05TapPau/HOTAS/Images/Frames.jpg

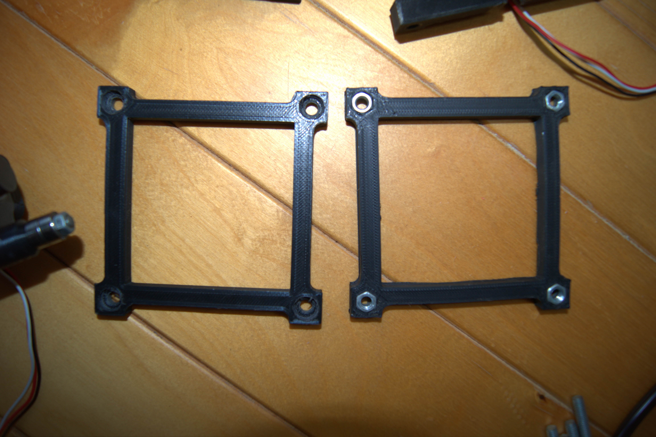
Images/Frames.jpg
