05TapPau/HOTAS/Images/Shell_poti.jpg

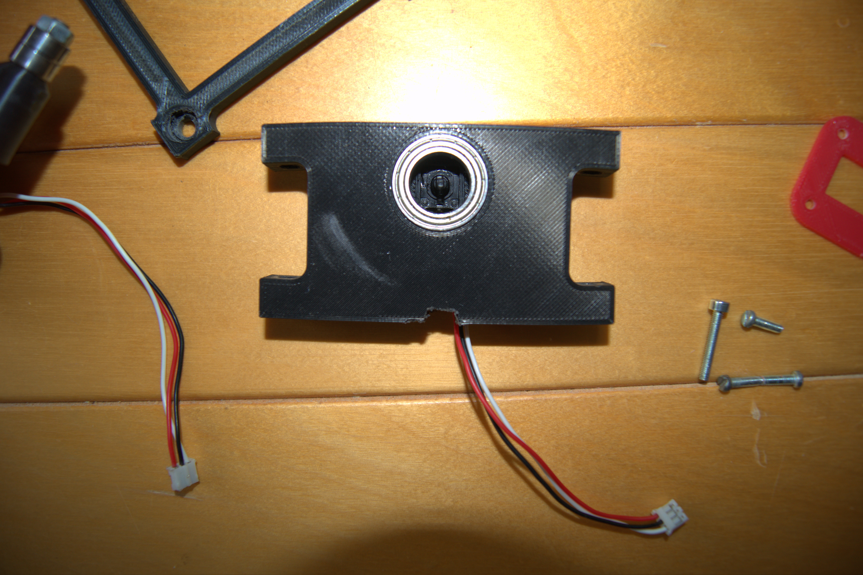
Images/Shell_poti.jpg
