05TapPau/HOTAS/Images/All parts.jpg

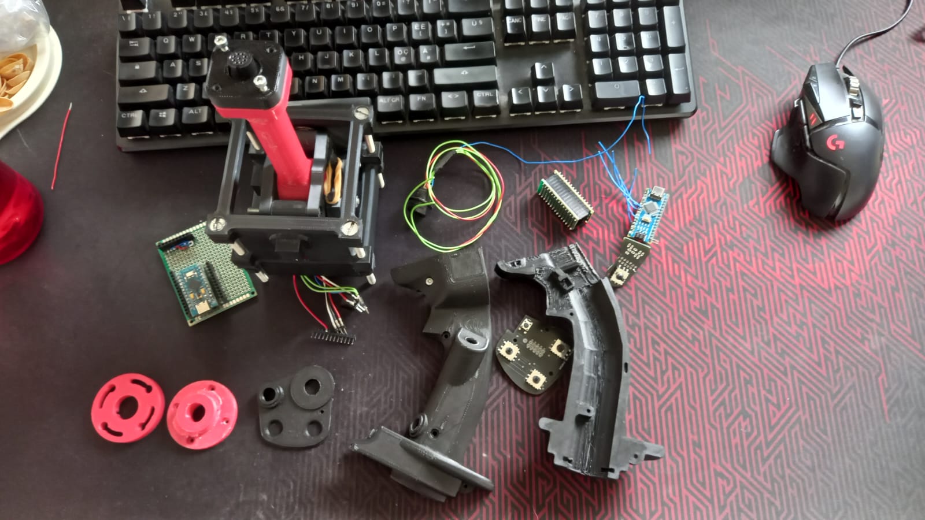
Images/All parts.jpg
