05TapPau/HOTAS/Images/all_parts_Gimbal.jpg

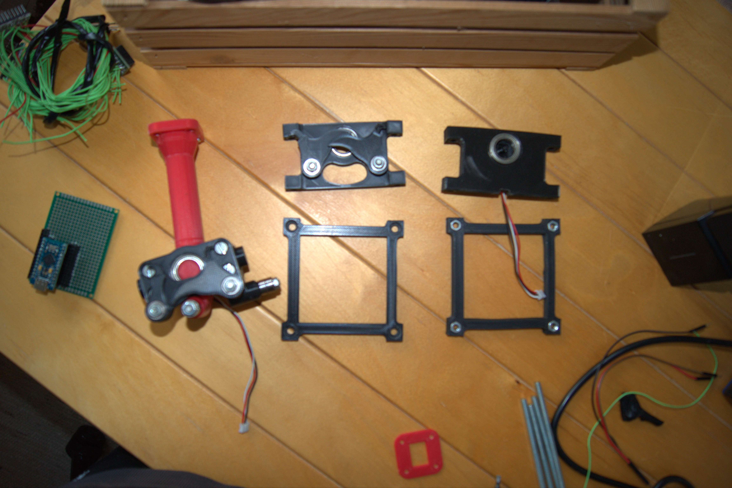
Images/all_parts_Gimbal.jpg
