05TapPau/HOTAS/ReadyToPrint_Gimbal/twiston_Spacer.stl

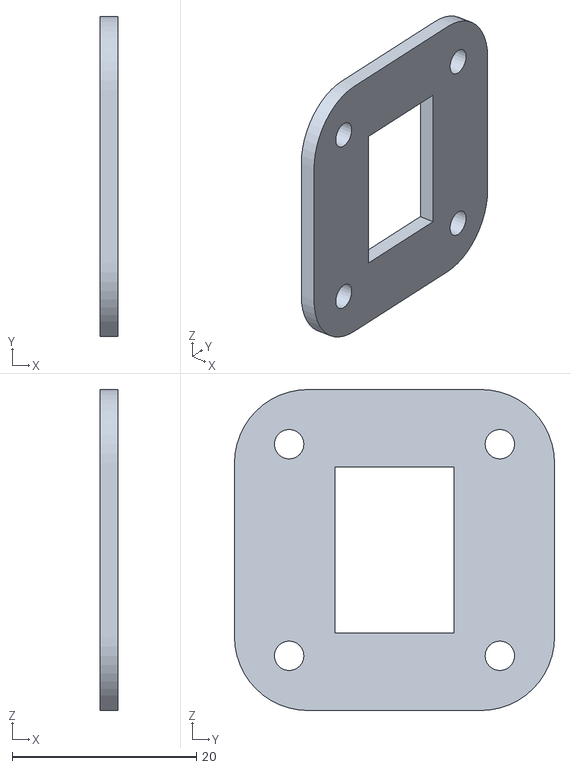
[picture p48: CAD file, 2024-05-22]
ReadyToPrint_Gimbal/twiston_Spacer.stl
2.00 x 34.8 x 34.9
