05TapPau/HOTAS/ReadyToPrint_Joystick/PinkieHolder.stl

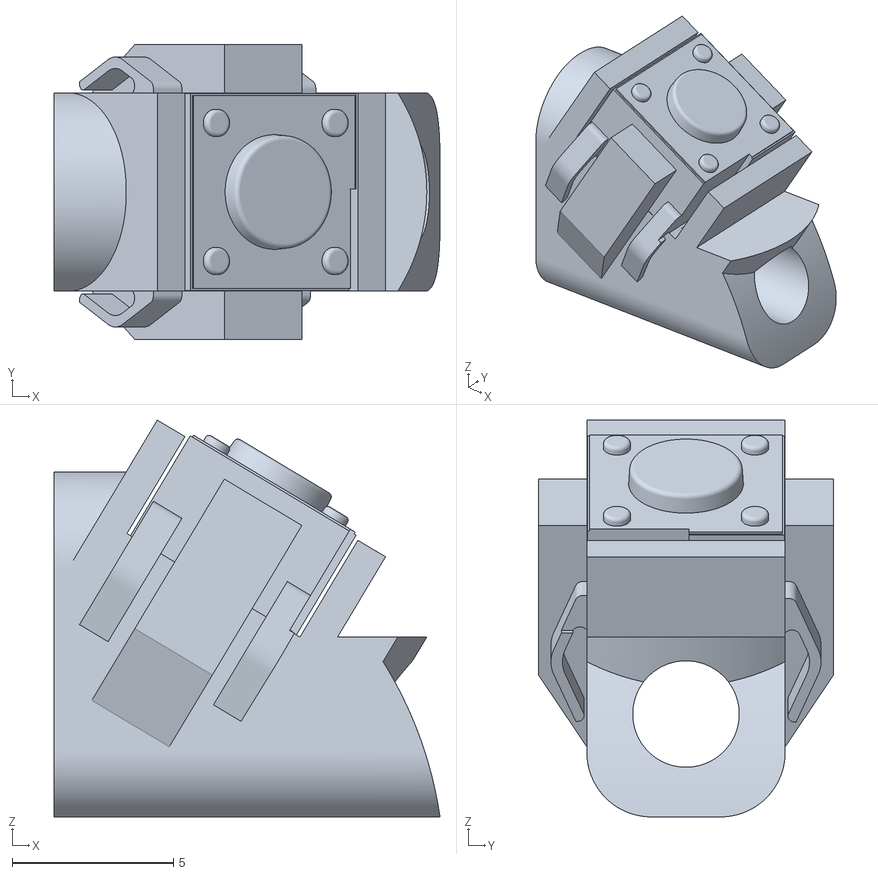
[picture p49: CAD file, 2024-05-22]
ReadyToPrint_Joystick/PinkieHolder.stl
12.0 x 9.15 x 12.3
