05TapPau/HOTAS/ReadyToPrint_Joystick/Top.stl

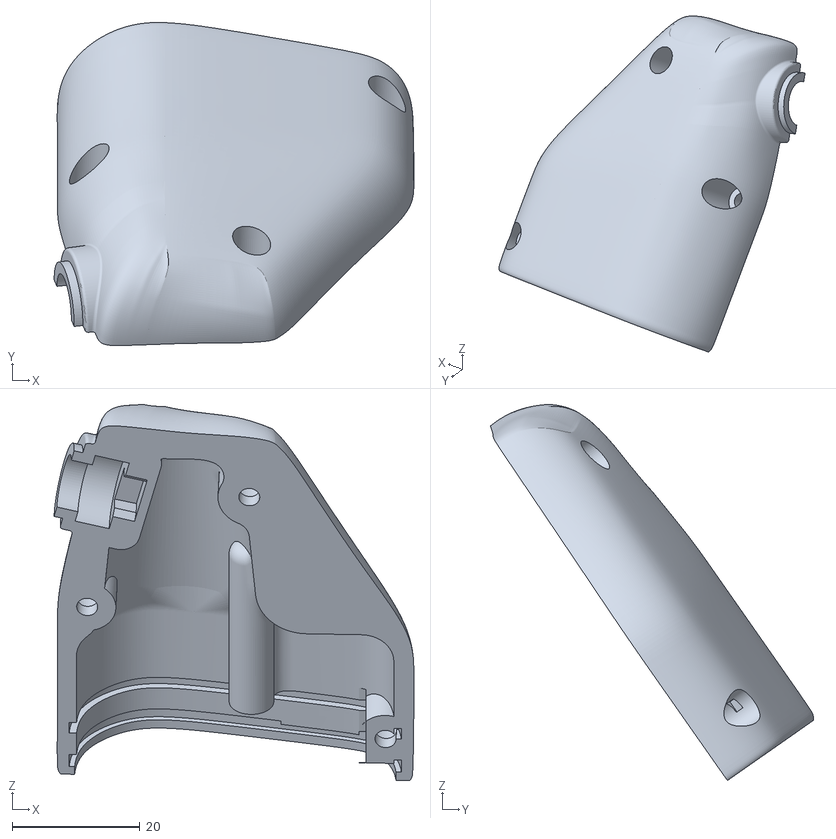
[picture p50: CAD file, 2024-05-22]
ReadyToPrint_Joystick/Top.stl
56.4 x 50.6 x 58.9
