05TapPau/HOTAS/ReadyToPrint_Gimbal/connector v4.stl

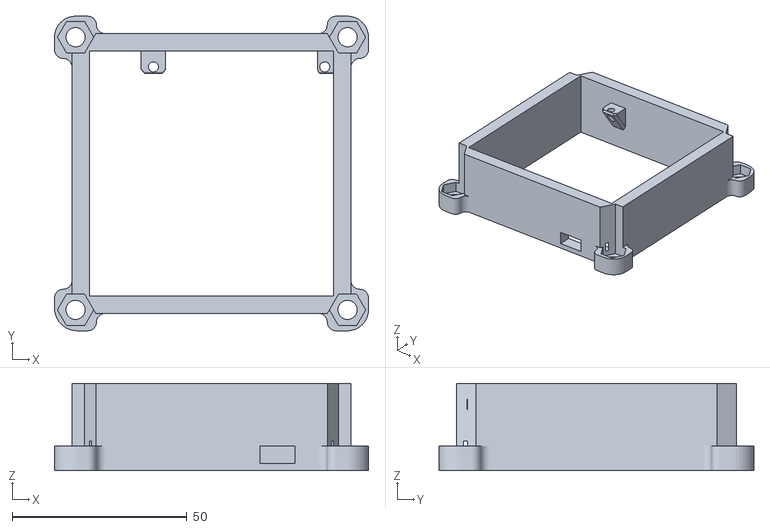
[picture p51: CAD file, 2024-05-22]
ReadyToPrint_Gimbal/connector v4.stl
89.8 x 90.0 x 25.0
