05TapPau/HOTAS/ReadyToPrint_Joystick/Pickle.stl

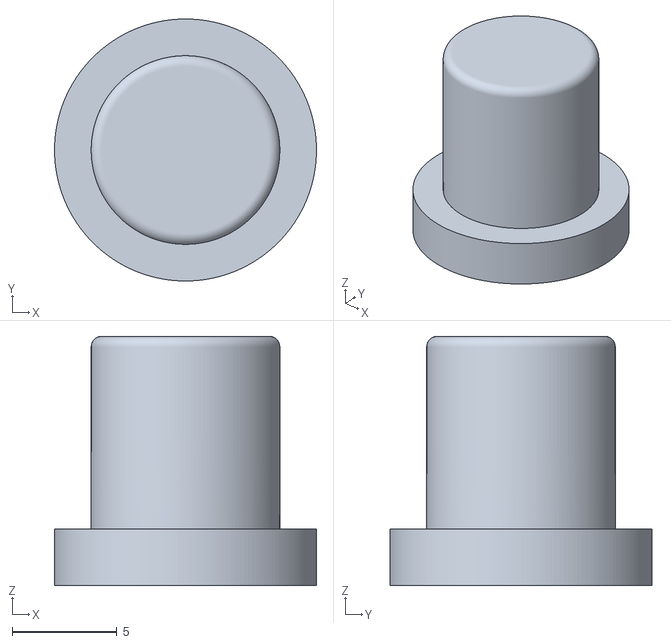
[picture p52: CAD file, 2024-05-22]
ReadyToPrint_Joystick/Pickle.stl
12.5 x 12.5 x 11.9
