05TapPau/HOTAS/ReadyToPrint_Joystick/NWS.stl

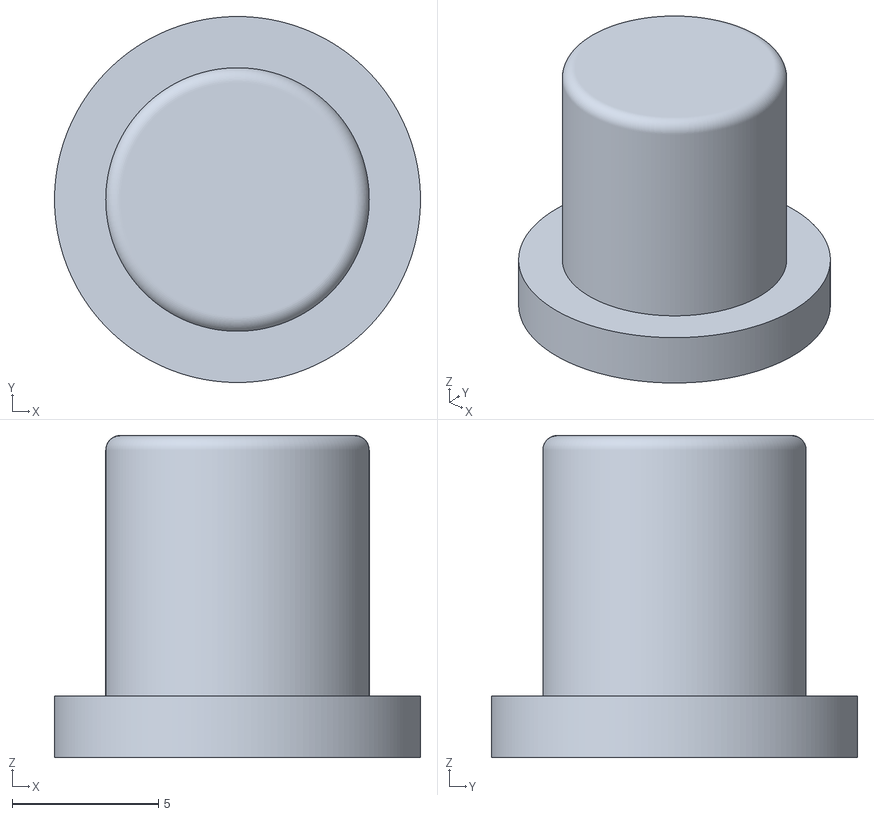
[picture p53: CAD file, 2024-05-22]
ReadyToPrint_Joystick/NWS.stl
12.5 x 12.5 x 11.0
