05TapPau/HOTAS/ReadyToPrint_Joystick/TMS_Hat.stl

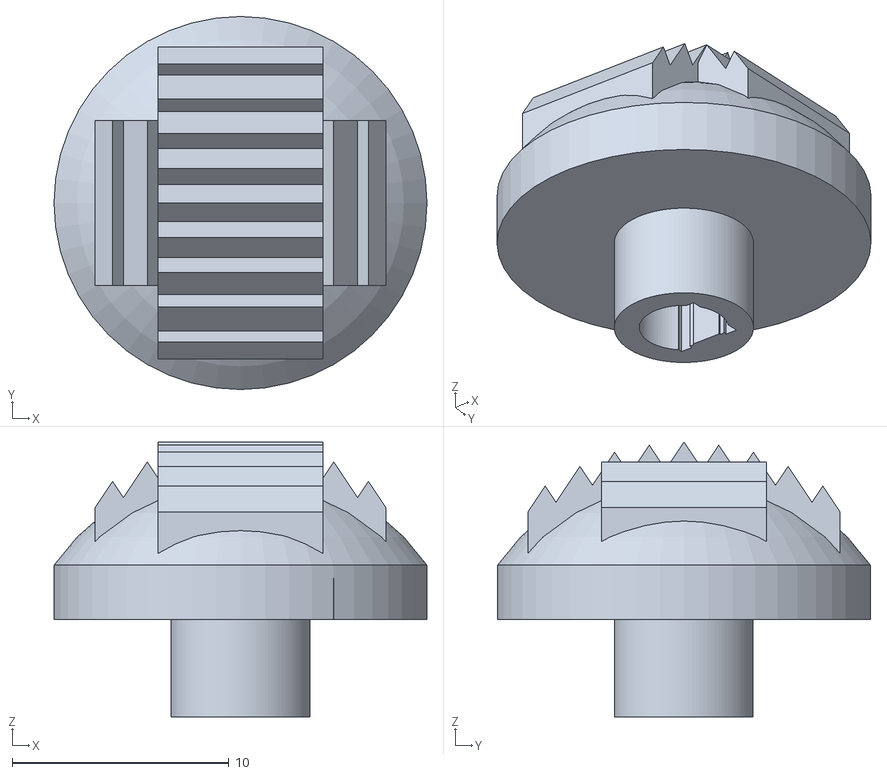
[picture p54: CAD file, 2024-05-22]
ReadyToPrint_Joystick/TMS_Hat.stl
17.2 x 17.2 x 12.7
