05TapPau/HOTAS/Images/Assembly_01.jpg

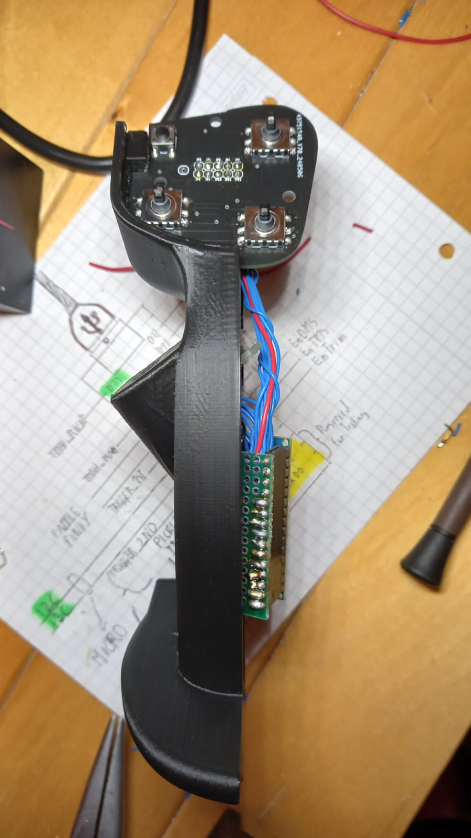
Images/Assembly_01.jpg
