05TapPau/HOTAS/Images/Assembly_02.jpg

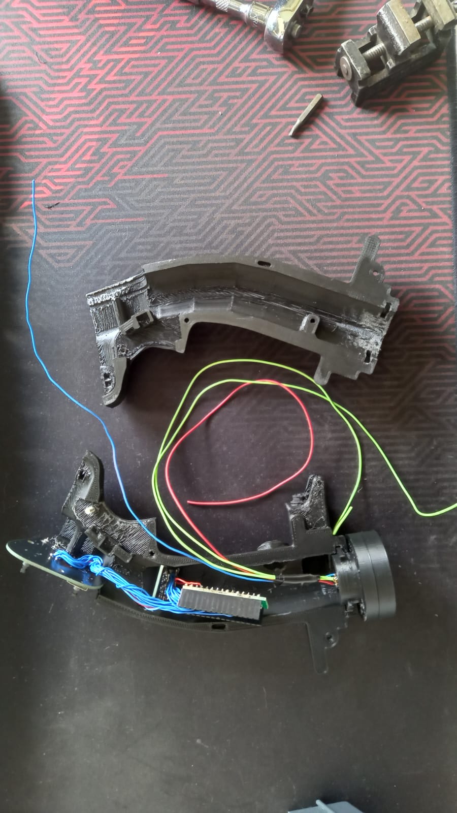
Images/Assembly_02.jpg
