05TapPau/HOTAS/Images/Assembly_04.jpg

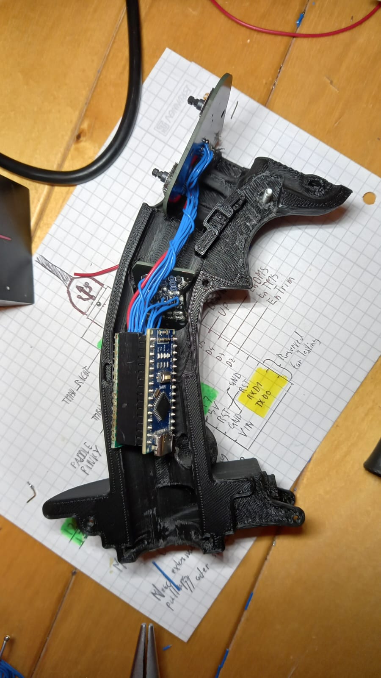
Images/Assembly_04.jpg
