05TapPau/HOTAS/Images/Testing_02.jpg

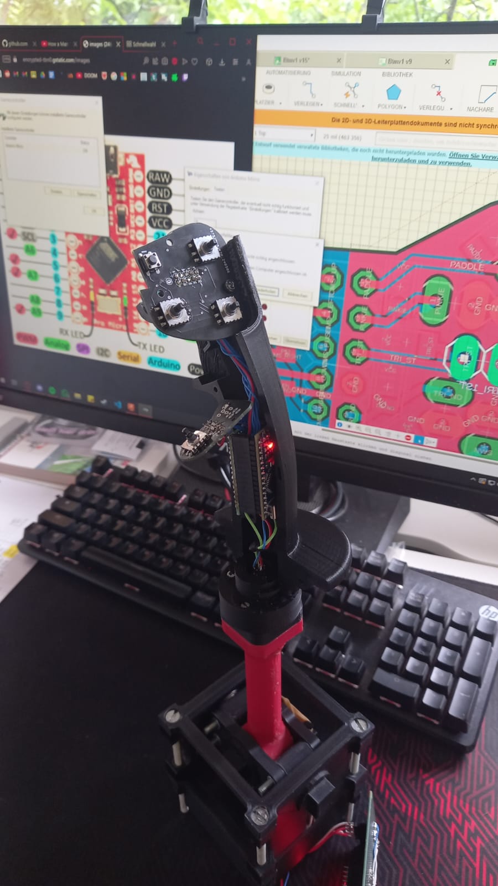
Images/Testing_02.jpg
